HailStorm32/Word-n-Seek_ECE_411/Documents/Team 5 - Gantt Chart - WordnSeek (20241107).pdf

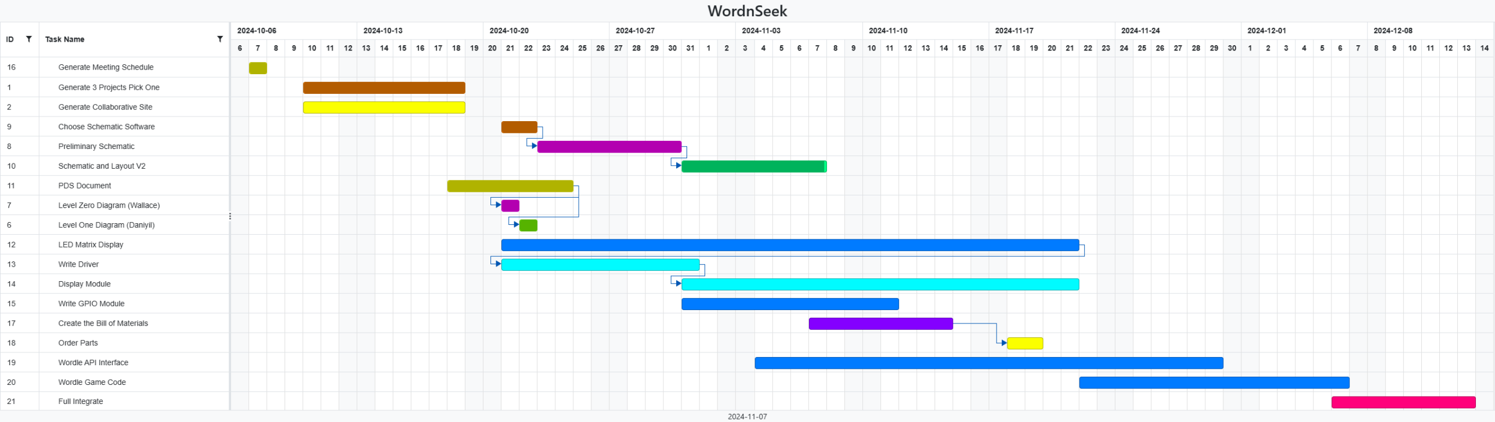
[picture p13: page 1]
