HailStorm32/Word-n-Seek_ECE_411/Documents/Team 5 - HW Wk 06 - Show off Your Breadboard Prototype (Group).pdf

ECE 411
Andrew Greenberg
11/04/2024

## Team 5 Show off Your Breadboard Prototype Assignment

Bucanan Howard, Daniyil Kashkan, Demetrius Van Sickle, Mohammed Alreshoud, and Wallace McKenzie

Team 5 GitHub repository: https://github.com/HailStorm32/Word-n-Seek/tree/main

At this point, our breadboard prototype looks and works as shown in the pictures below.

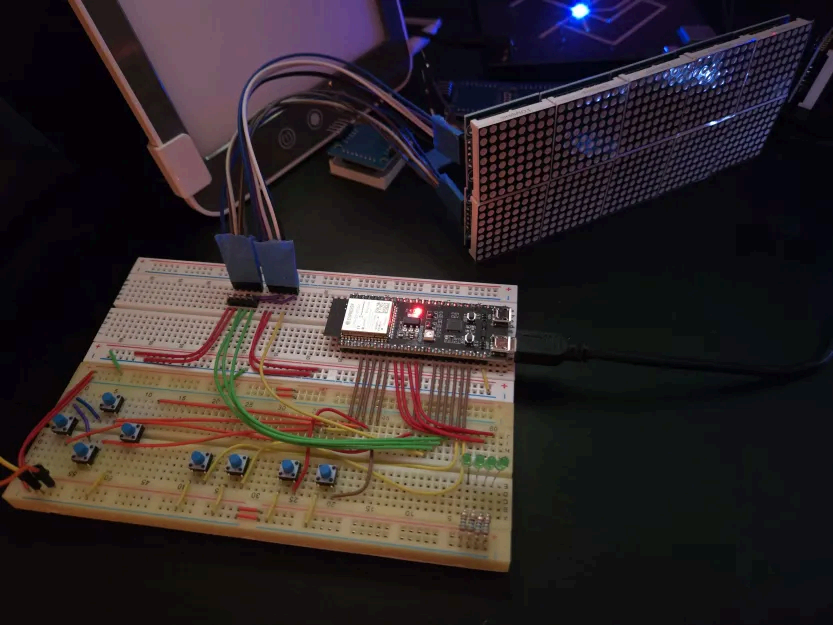
[picture p14: figure]

Figure 1. Breadboard Prototype Design.

1

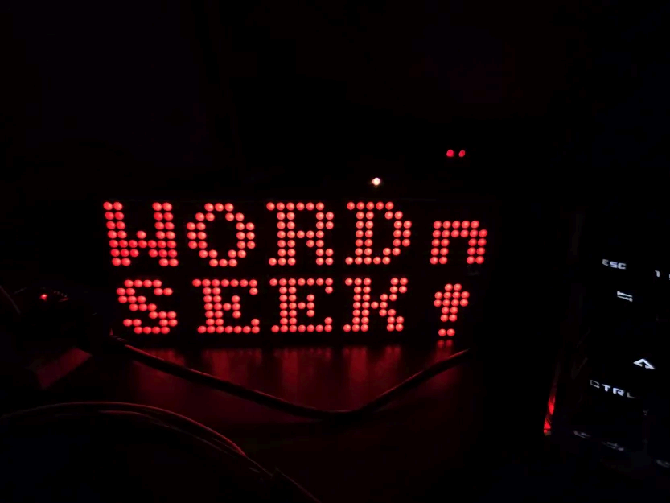
[picture p15: figure]

Figure 2. Word-n-Seek welcome screen.

To see videos of the working project, see our GitHub repository.

Video #1:
https://github.com/HailStorm32/Word-n-Seek/blob/main/Breadboard%20Prototype%20Videos/Full%20di splay%20boot%20up.mp4 (https://github.com/HailStorm32/Word-n-Seek/blob/main/Breadboard%20Prototype%20Videos/Full%20display%20boot%20up.mp4)

Video #2:
https://github.com/HailStorm32/Word-n-Seek/blob/main/Breadboard%20Prototype%20Videos/Scrolly%2 0(sequence%20test).mp4 (https://github.com/HailStorm32/Word-n-Seek/blob/main/Breadboard%20Prototype%20Videos/Scrolly%20(sequence%20test).mp4)

Video #3:
https://github.com/HailStorm32/Word-n-Seek/blob/main/Breadboard%20Prototype%20Videos/Word-n-S eek%20idle%20animation.mp4 (https://github.com/HailStorm32/Word-n-Seek/blob/main/Breadboard%20Prototype%20Videos/Word-n-Seek%20idle%20animation.mp4)

Video #4:
https://github.com/HailStorm32/Word-n-Seek/blob/main/Breadboard%20Prototype%20Videos/Word-n-S eek%20start%20sequence.mp4 (https://github.com/HailStorm32/Word-n-Seek/blob/main/Breadboard%20Prototype%20Videos/Word-n-Seek%20start%20sequence.mp4)

2
