HailStorm32/Word-n-Seek_ECE_411/Documents/Breadboard Prototype Photos/20241031_224848.webp

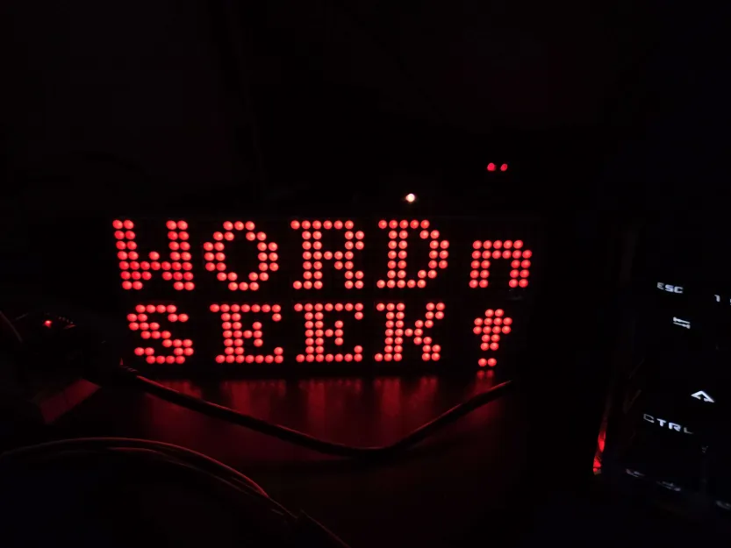
Documents/Breadboard Prototype Photos/20241031_224848.webp
