HailStorm32/Word-n-Seek_ECE_411/BoardFiles/WordNSeekPCBVer2Bottom.pdf

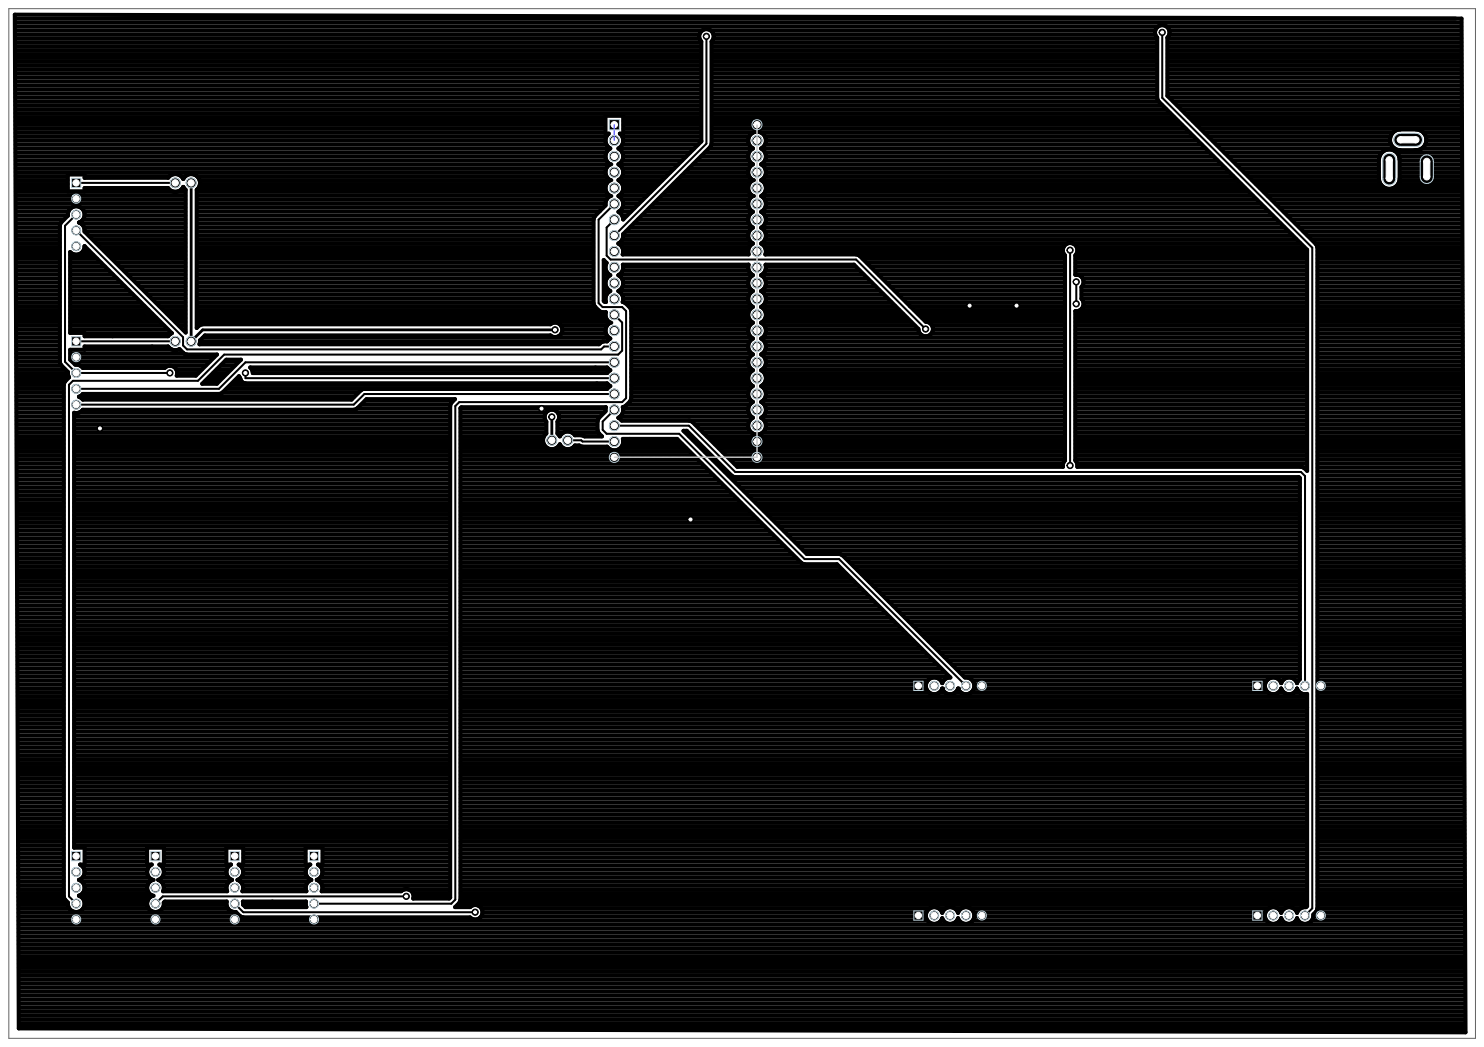
[picture p26: page 1]
