HailStorm32/Word-n-Seek_ECE_411/BoardFiles/WordNSeekPCBVer2Top.pdf

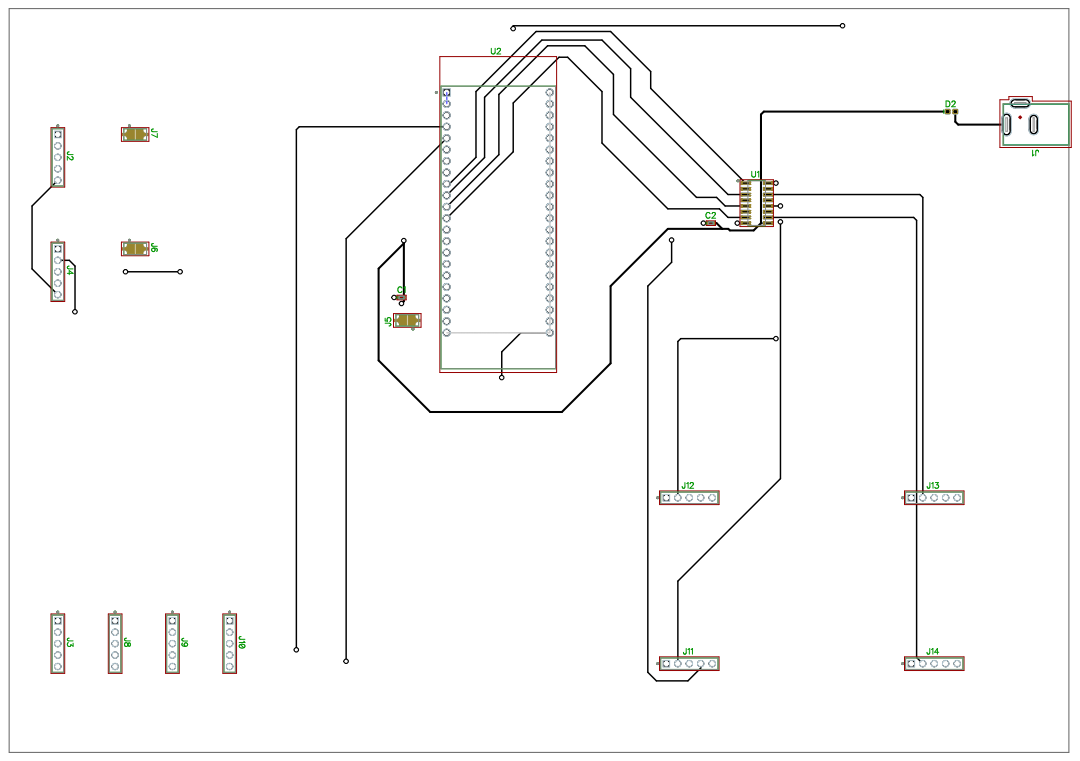
[picture p27: page 1]
